greenjacketgirl/Solar_Charger/Media/blockdiagram1.png

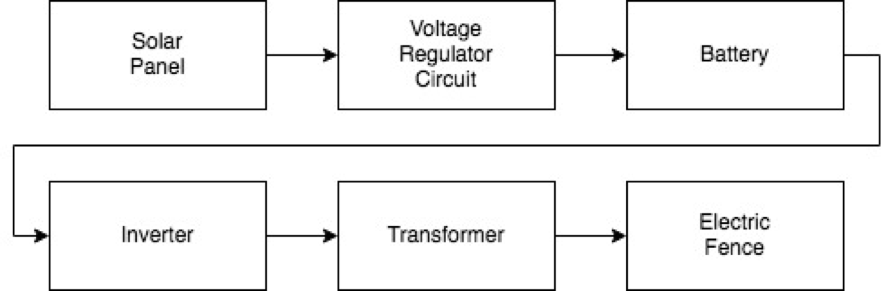
Media/blockdiagram1.png
