greenjacketgirl/Solar_Charger/Media/boardtoasteroven.jpg

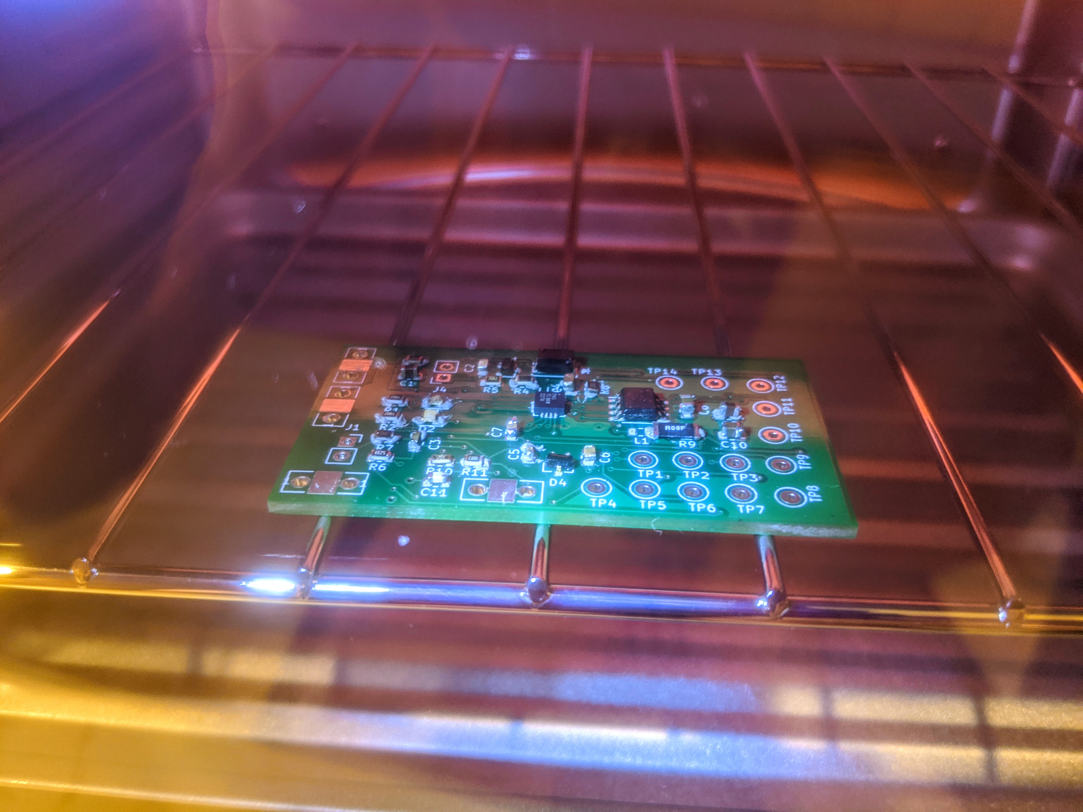
Media/boardtoasteroven.jpg
