greenjacketgirl/Solar_Charger/Media/boardtoasterovenfinish.jpg

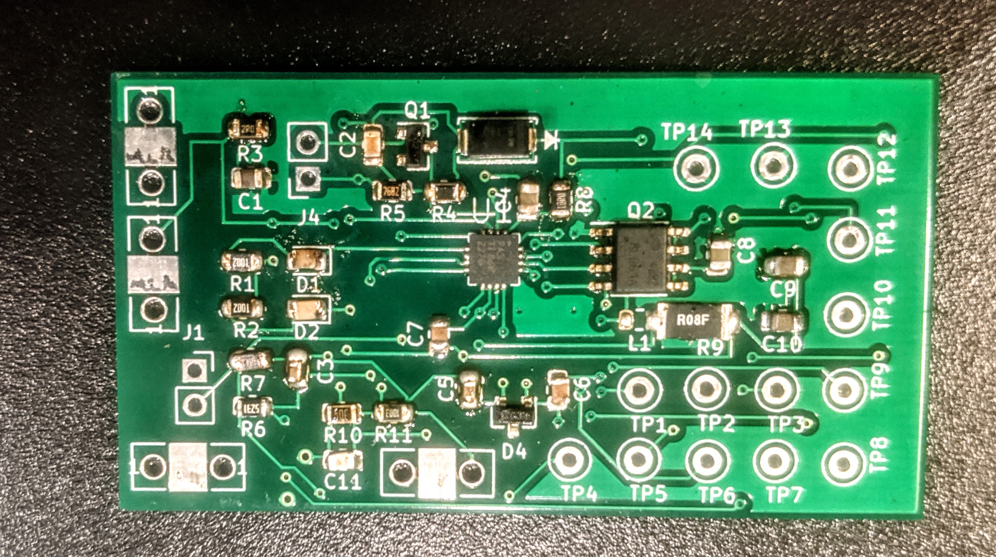
Media/boardtoasterovenfinish.jpg
