greenjacketgirl/Solar_Charger/Media/buckconverterdiagram.png

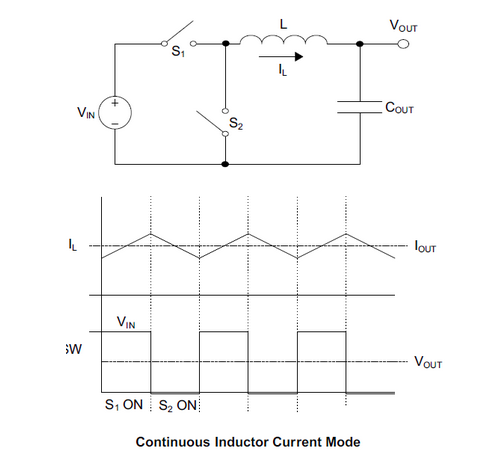
Media/buckconverterdiagram.png
