greenjacketgirl/Solar_Charger/Media/burnttrace.jpg

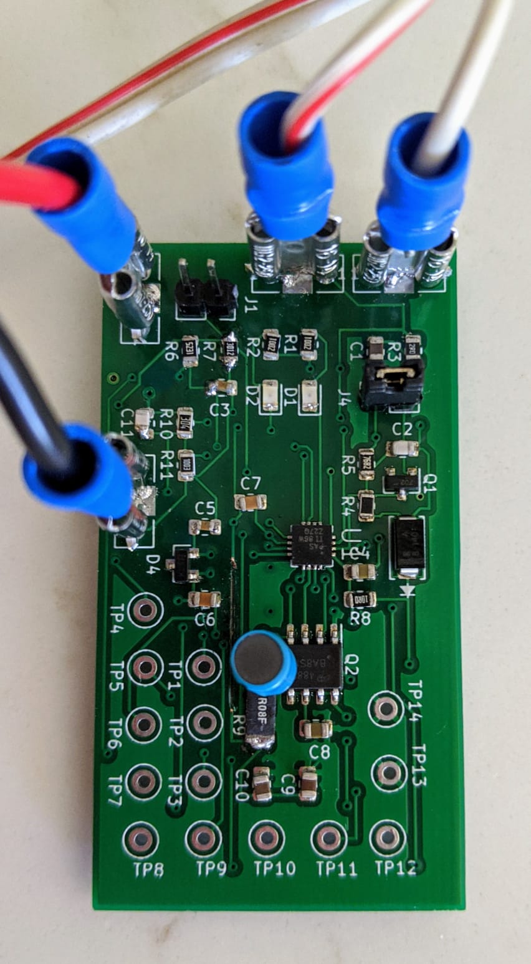
Media/burnttrace.jpg
