greenjacketgirl/Solar_Charger/Media/chargersummarytable.png

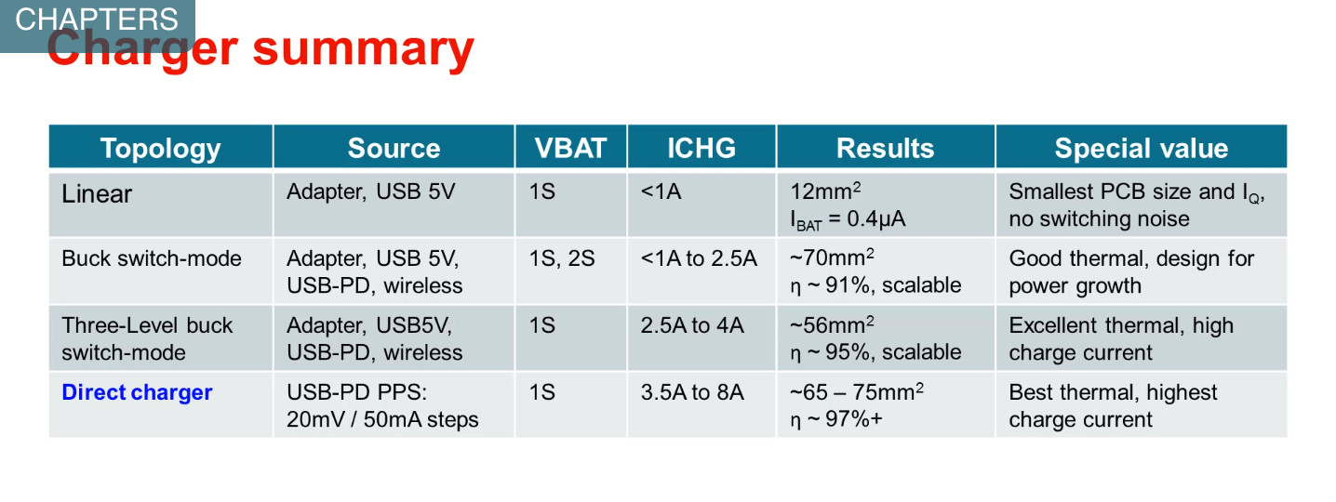
Media/chargersummarytable.png
