greenjacketgirl/Solar_Charger/Media/EVM.jpg

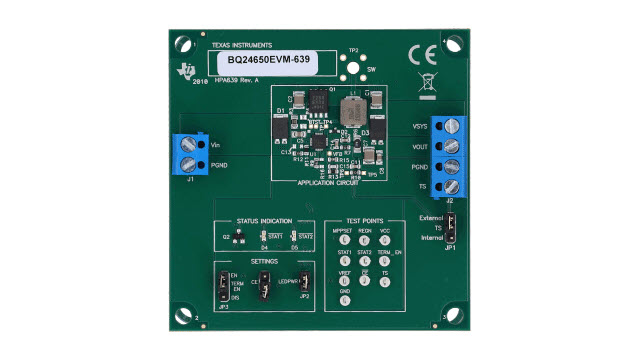
Media/EVM.jpg
