greenjacketgirl/Solar_Charger/Media/hidrivlodrive large time scale.png

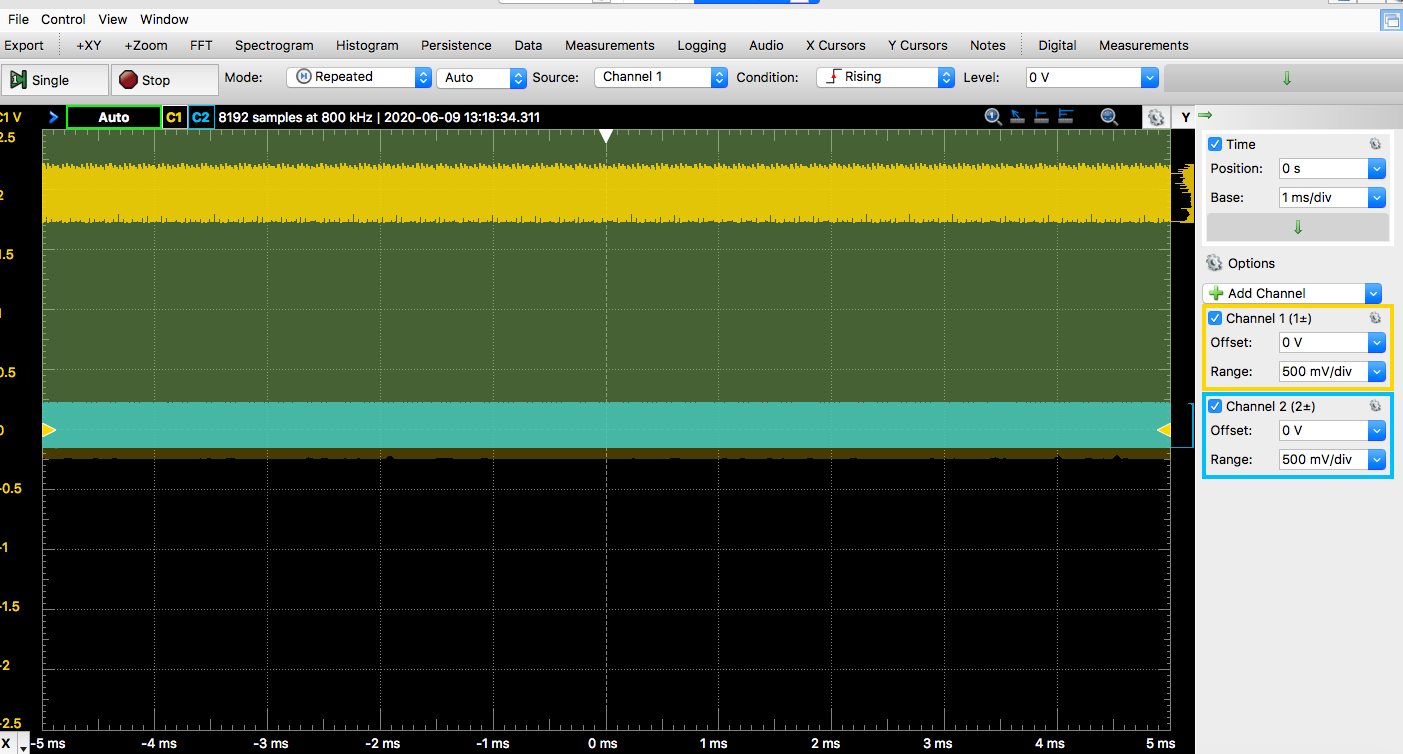
Media/hidrivlodrive large time scale.png
