greenjacketgirl/Solar_Charger/Media/LEDaddition2.jpg

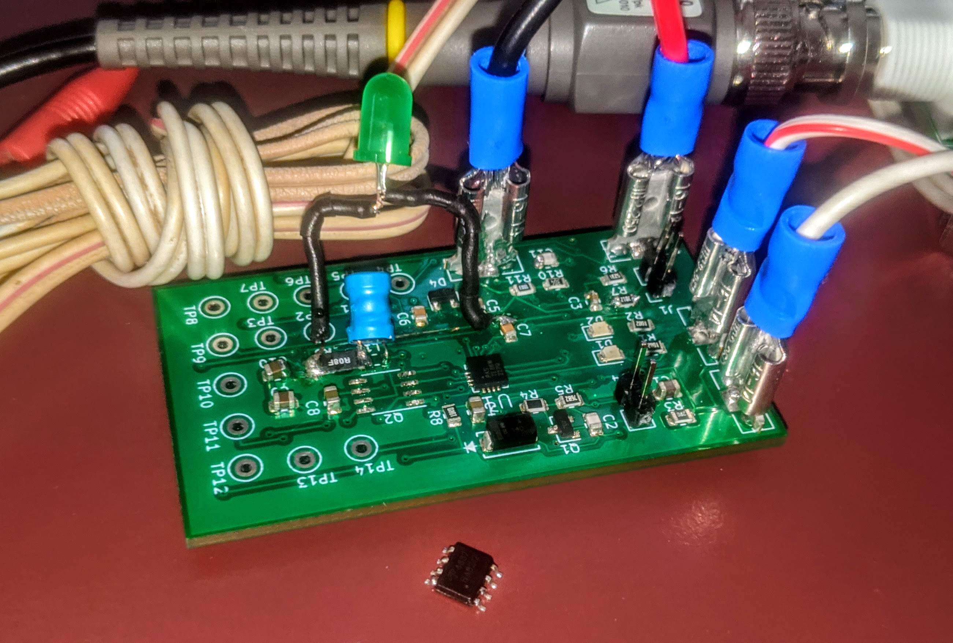
Media/LEDaddition2.jpg
