greenjacketgirl/Solar_Charger/Media/LEDadditon1.jpg

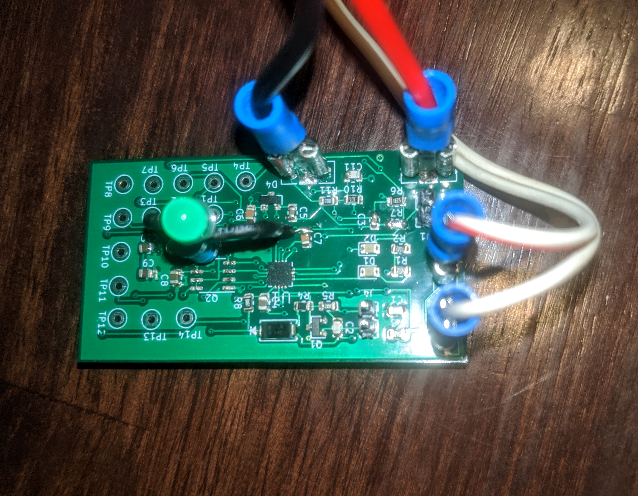
Media/LEDadditon1.jpg
