greenjacketgirl/Solar_Charger/Media/Lithium ion battery charge curve.png

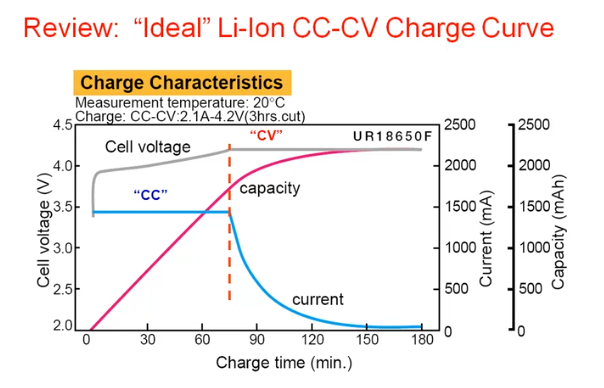
Media/Lithium ion battery charge curve.png
