greenjacketgirl/Solar_Charger/Media/Lithiumionbatterychargecurvepart2.png

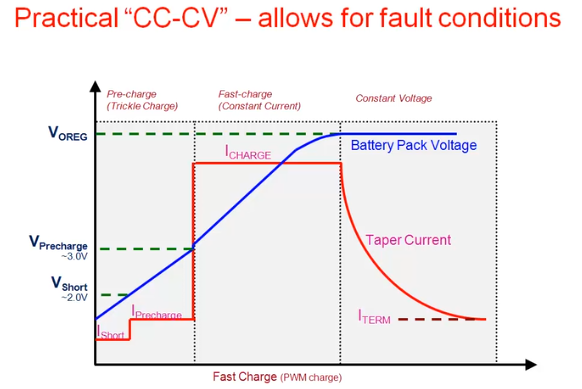
Media/Lithiumionbatterychargecurvepart2.png
