greenjacketgirl/Solar_Charger/Media/lodrivehidrive-batterydisconnected.png

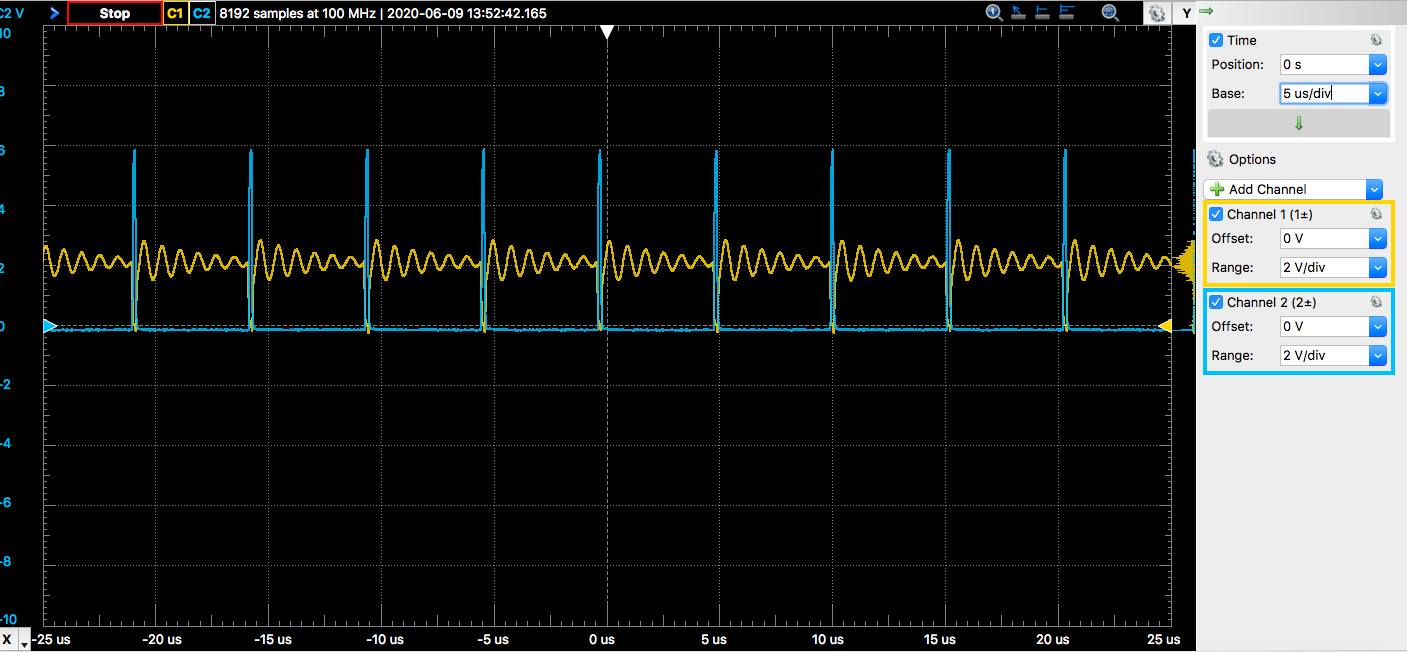
Media/lodrivehidrive-batterydisconnected.png
