greenjacketgirl/Solar_Charger/Media/lodrivhidrvshorttimescale-batteryconnected.png

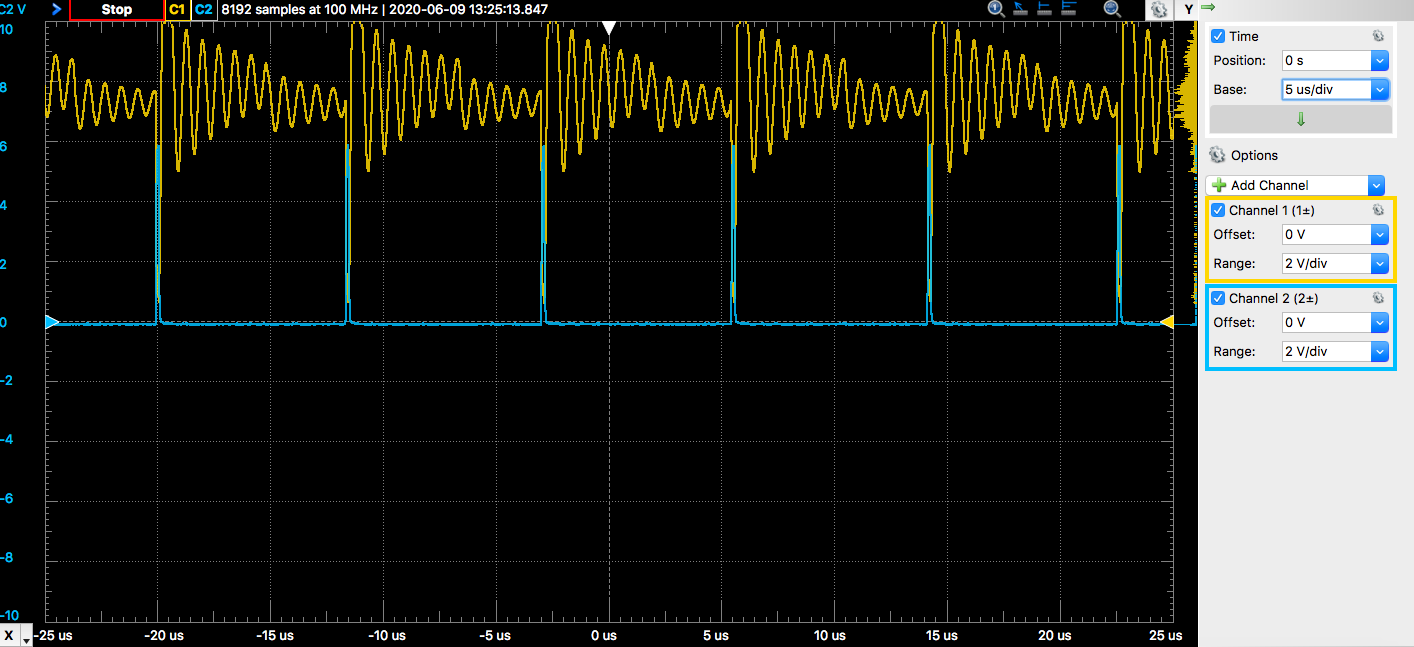
Media/lodrivhidrvshorttimescale-batteryconnected.png
