greenjacketgirl/Solar_Charger/Media/MPPToptions.png

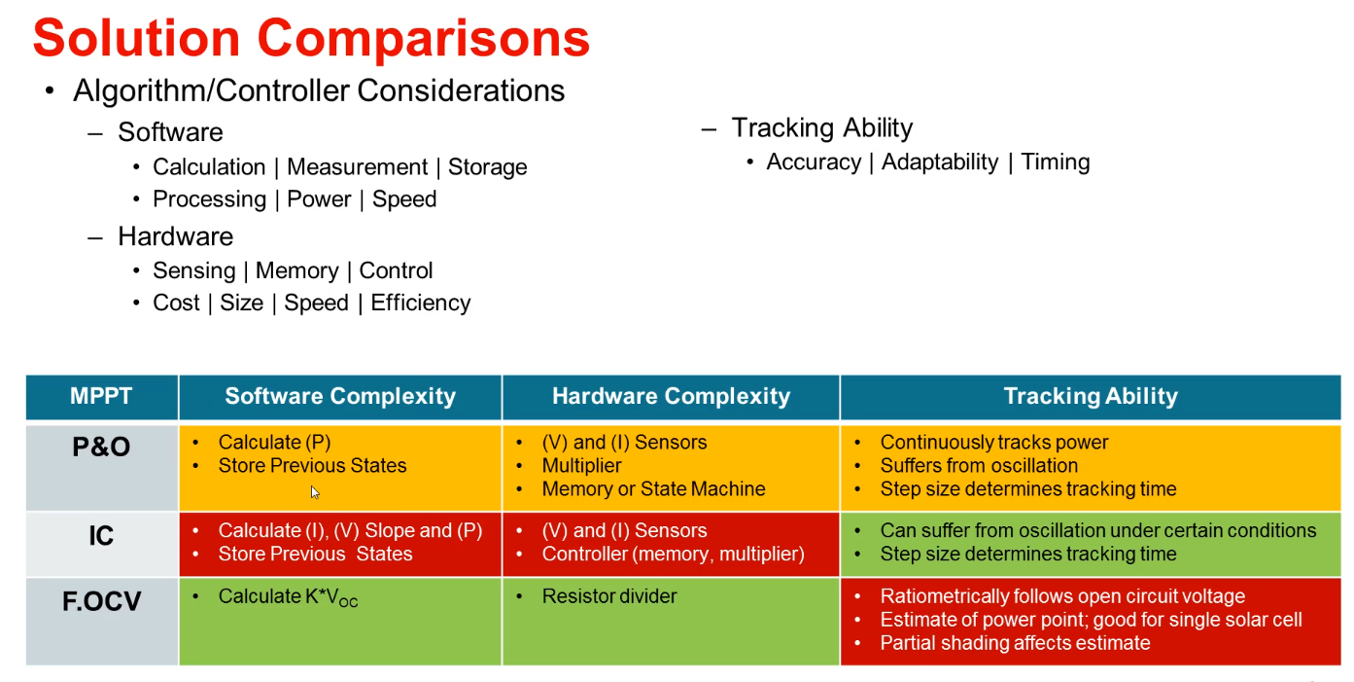
Media/MPPToptions.png
