greenjacketgirl/Solar_Charger/Media/outsidetesting.jpg

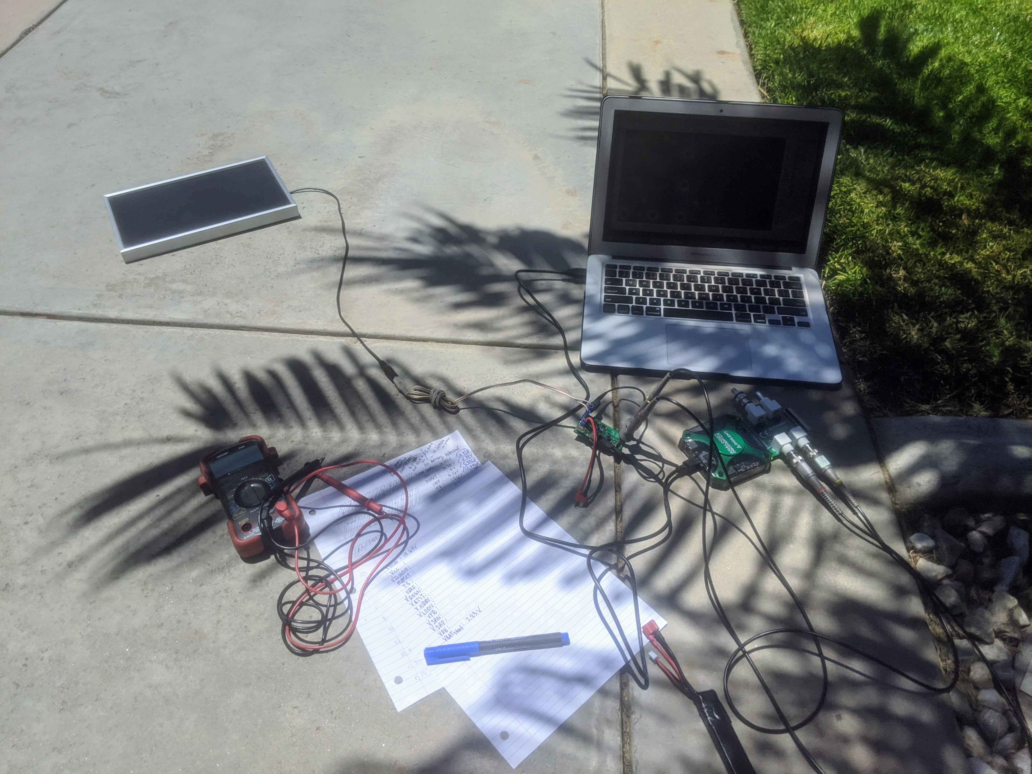
Media/outsidetesting.jpg
