greenjacketgirl/Solar_Charger/Media/placeparts.jpg

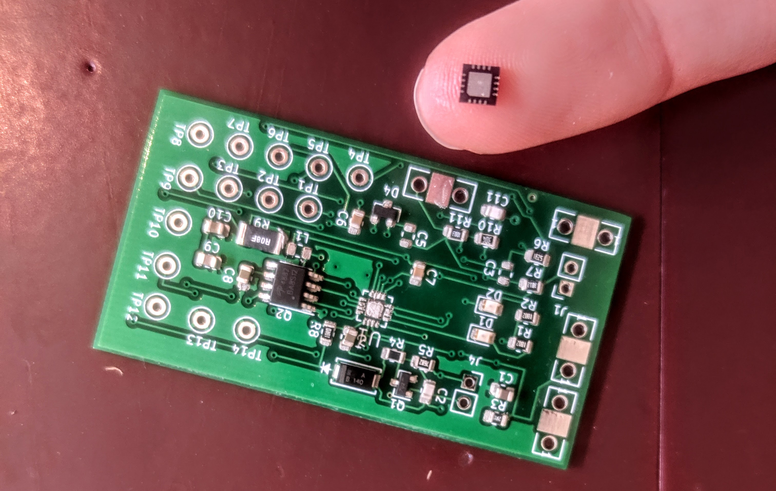
Media/placeparts.jpg
