greenjacketgirl/Solar_Charger/Media/Screenshot 2020-06-09 19.27.28.png

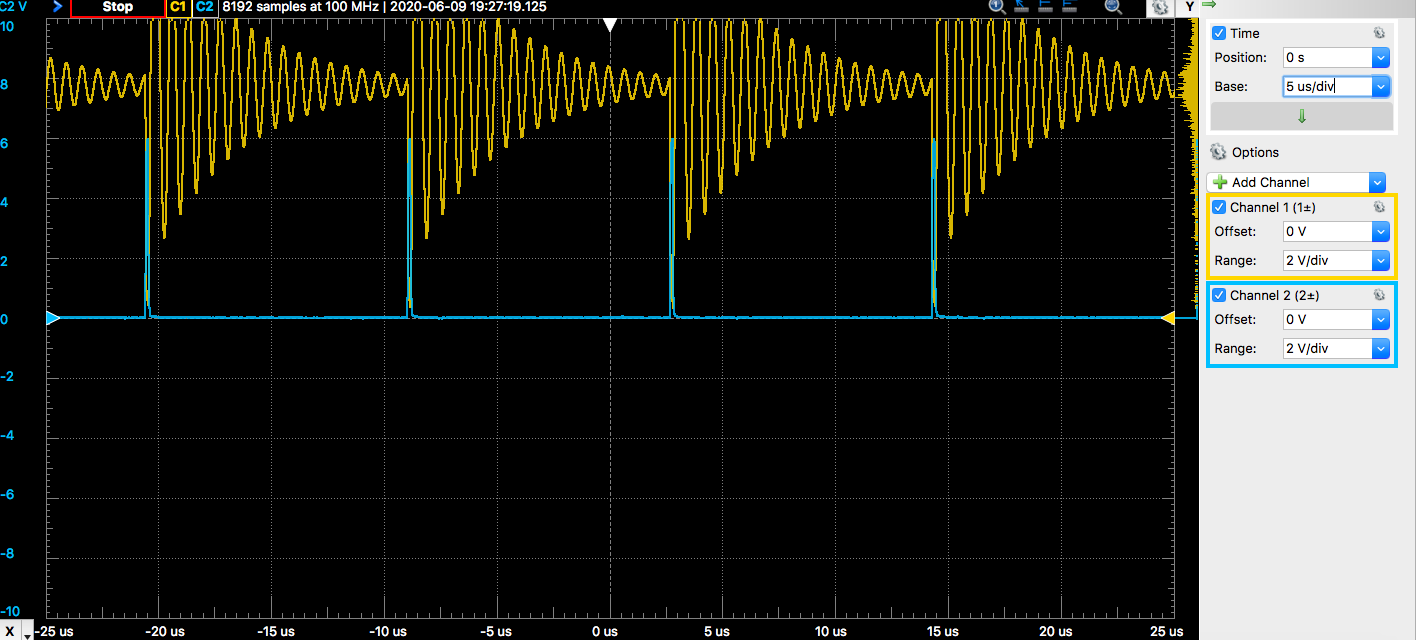
Media/Screenshot 2020-06-09 19.27.28.png
