greenjacketgirl/Solar_Charger/Media/Screenshot 2020-06-09 19.39.03.png

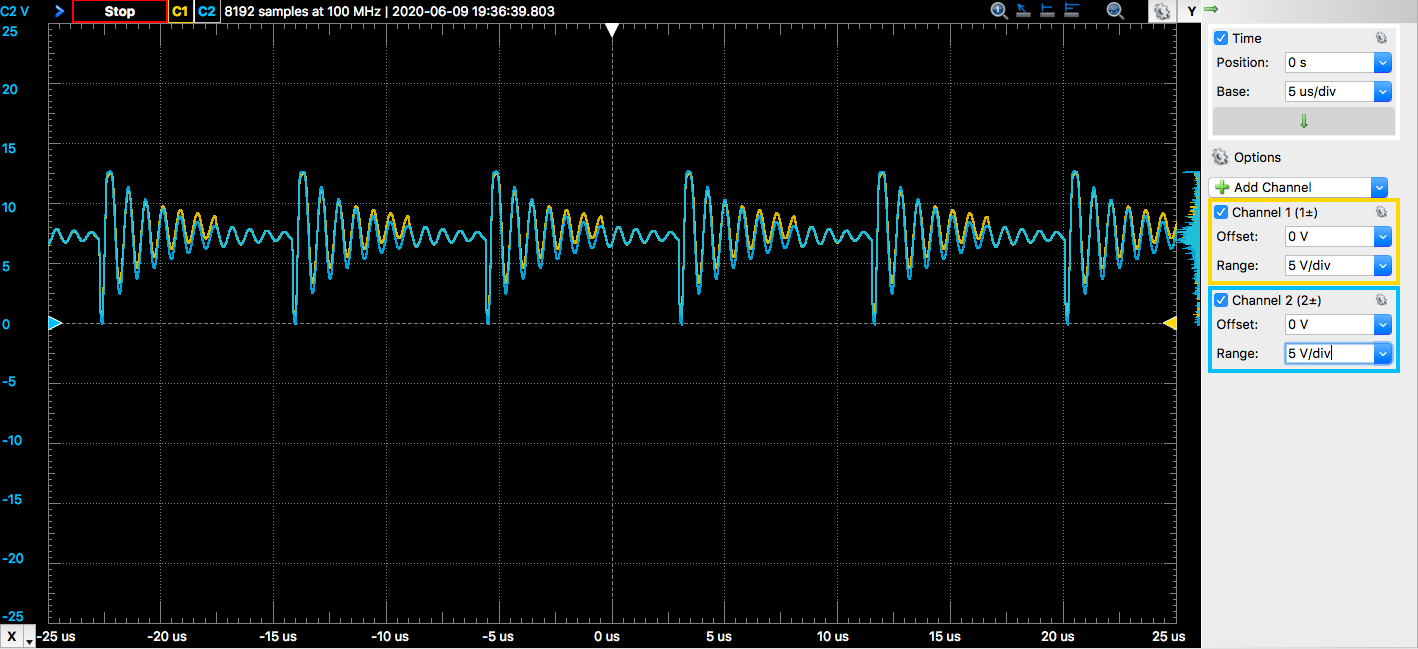
Media/Screenshot 2020-06-09 19.39.03.png
