greenjacketgirl/Solar_Charger/Media/Screenshot 2020-06-11 10.59.36.png

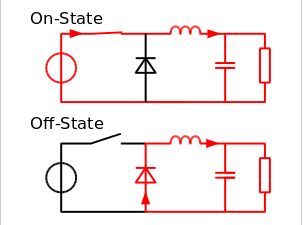
Media/Screenshot 2020-06-11 10.59.36.png
