greenjacketgirl/Solar_Charger/Media/typicalapplication.png

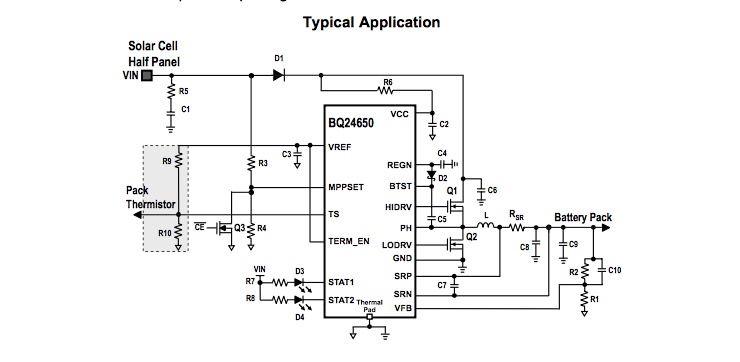
Media/typicalapplication.png
