greenjacketgirl/Solar_Charger/Media/requiredmaterials.jpg

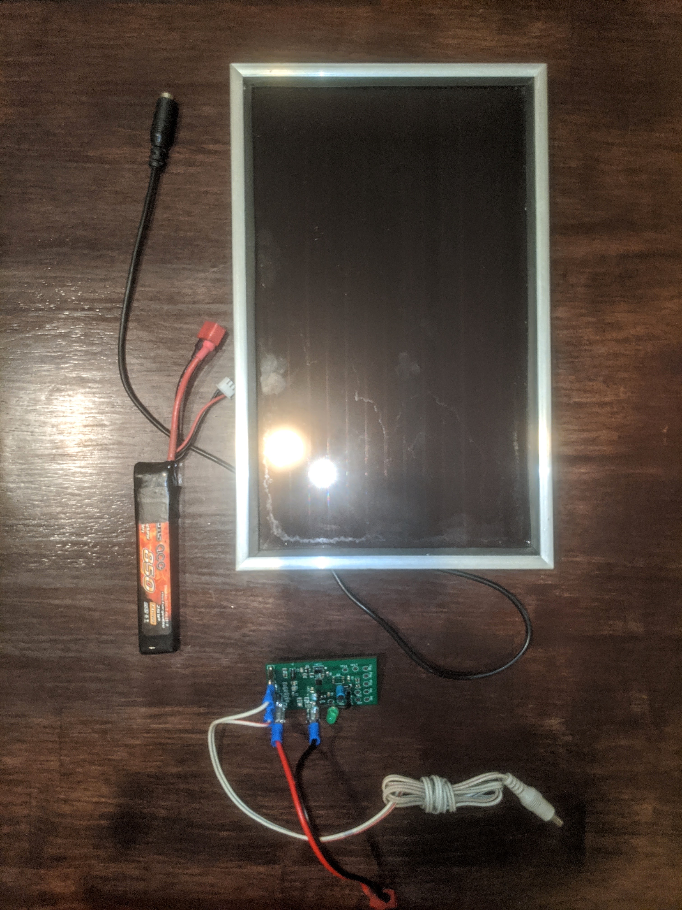
Media/requiredmaterials.jpg
