greenjacketgirl/Solar_Charger/Media/boardbuildpart2.jpg

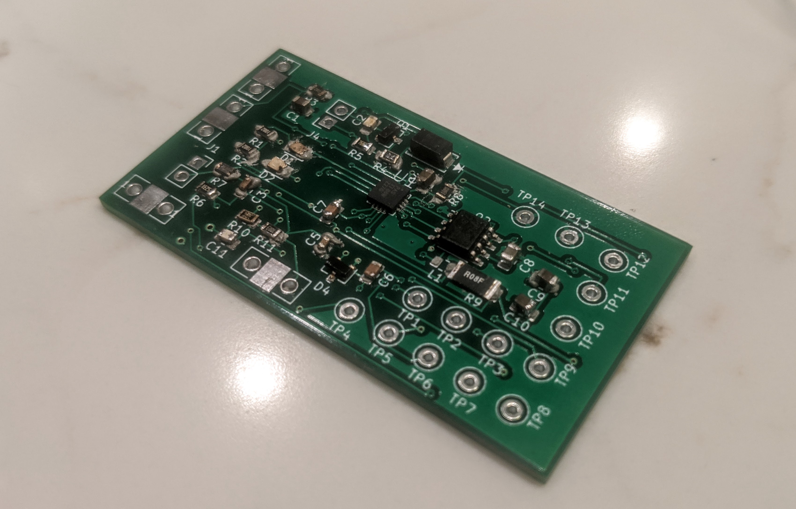
Media/boardbuildpart2.jpg
