greenjacketgirl/Solar_Charger/Media/completeboardbuild2.jpg

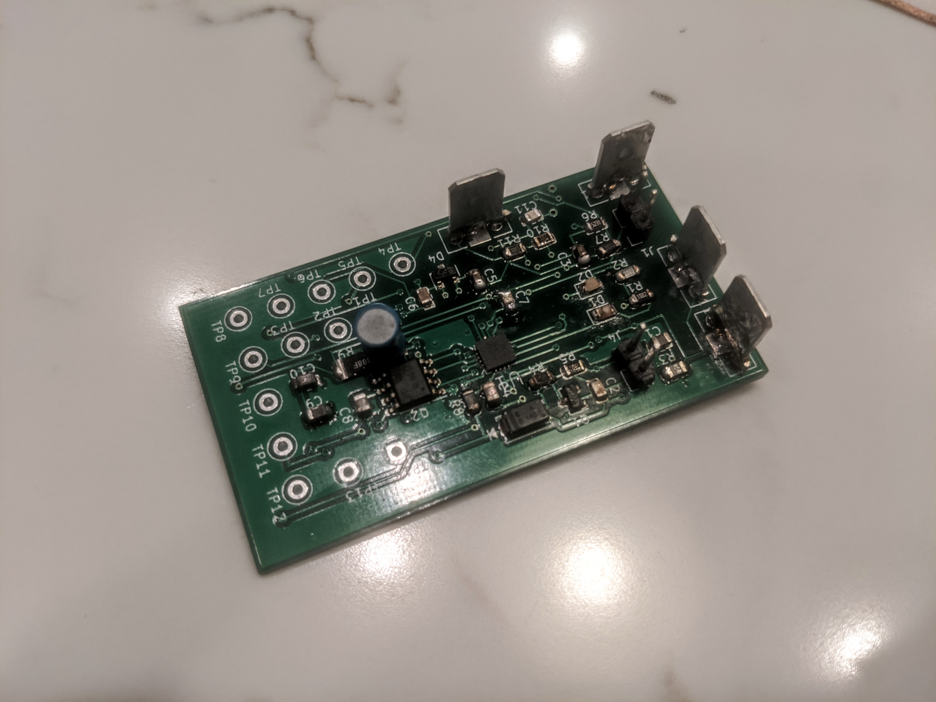
Media/completeboardbuild2.jpg
